LucaKrause1/CICIserlohn/PiScripts/Projection/generateImg/image.png

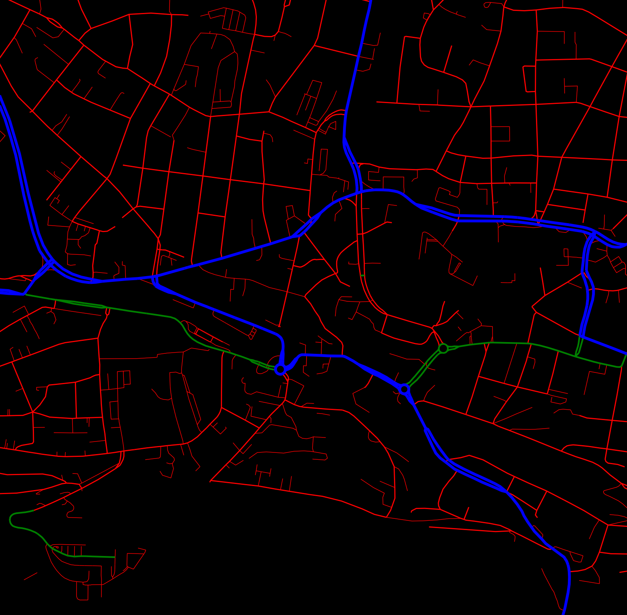
PiScripts/Projection/generateImg/image.png
