LucaKrause1/CICIserlohn/PiScripts/Projection/img/colorAllStreets.png

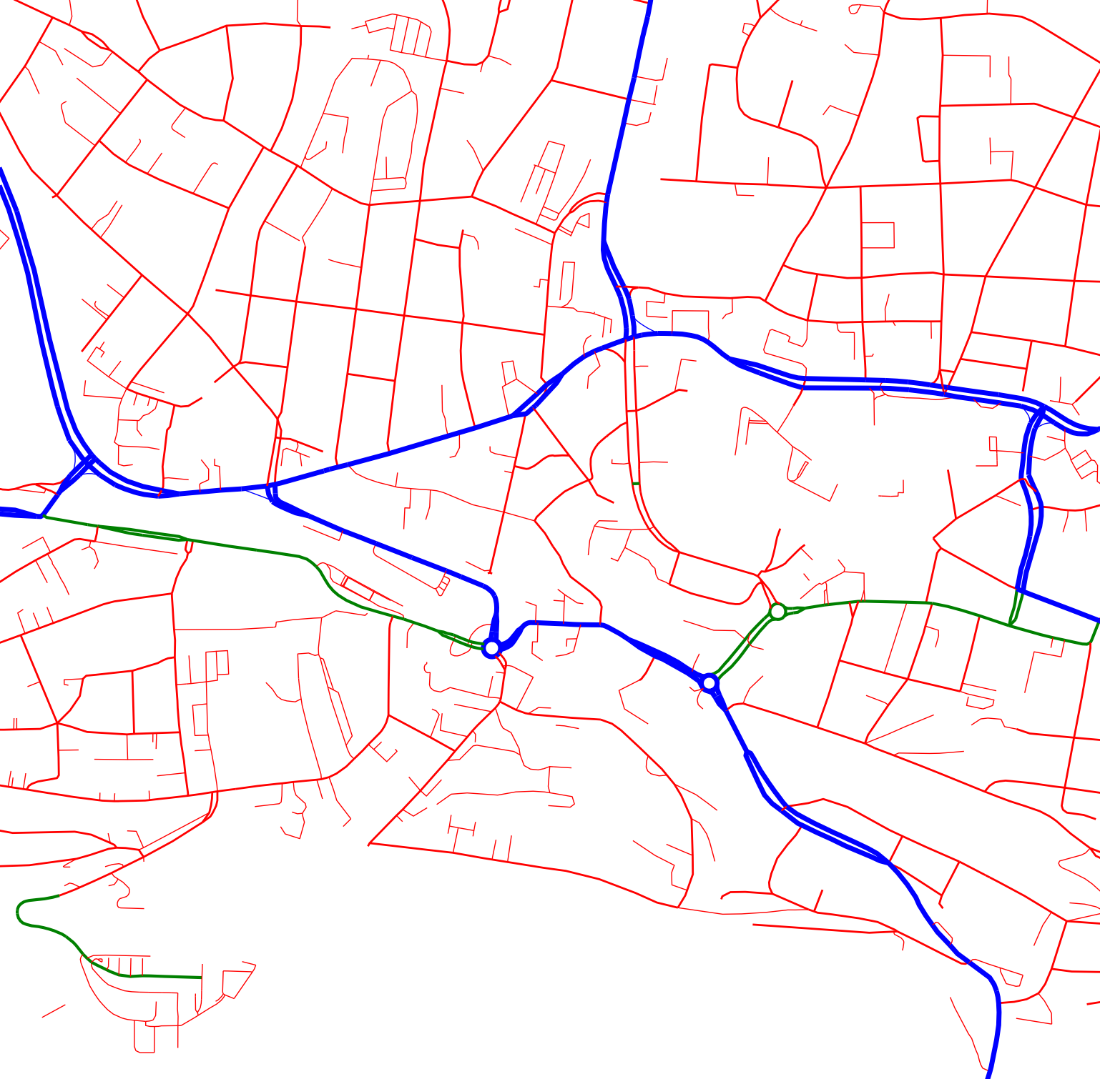
PiScripts/Projection/img/colorAllStreets.png
