LucaKrause1/CICIserlohn/PiScripts/Projection/img/colorBus.png

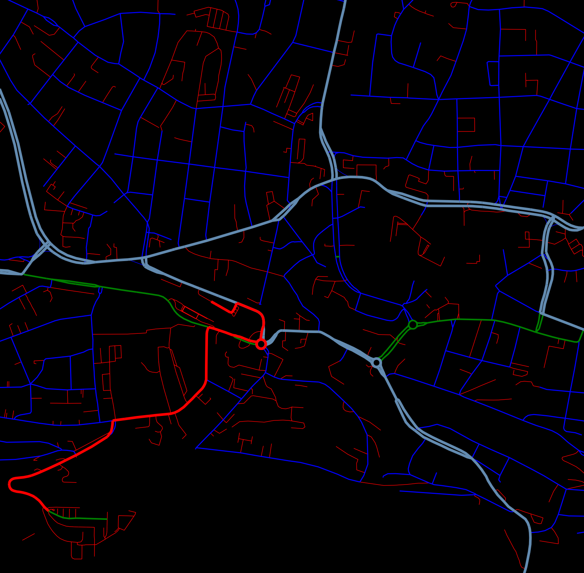
PiScripts/Projection/img/colorBus.png
