LucaKrause1/CICIserlohn/PiScripts/Projection/img/greyTree.png

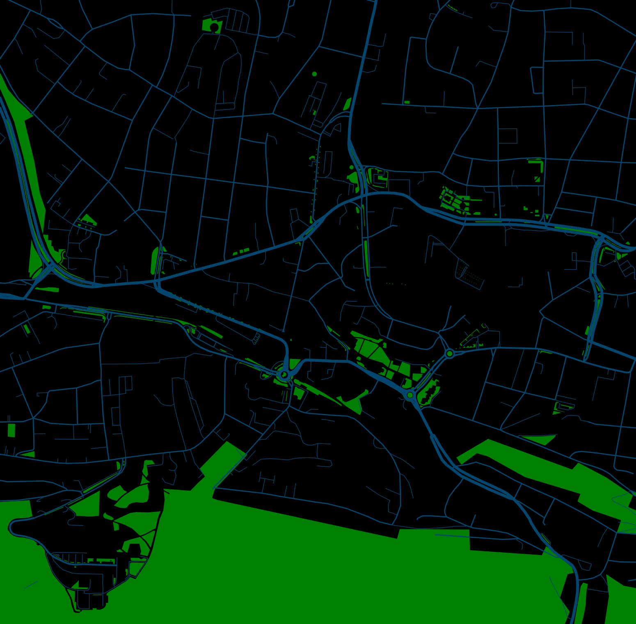
PiScripts/Projection/img/greyTree.png
