LucaKrause1/CICIserlohn/PiScripts/Projection/img/infoabus1.jpg

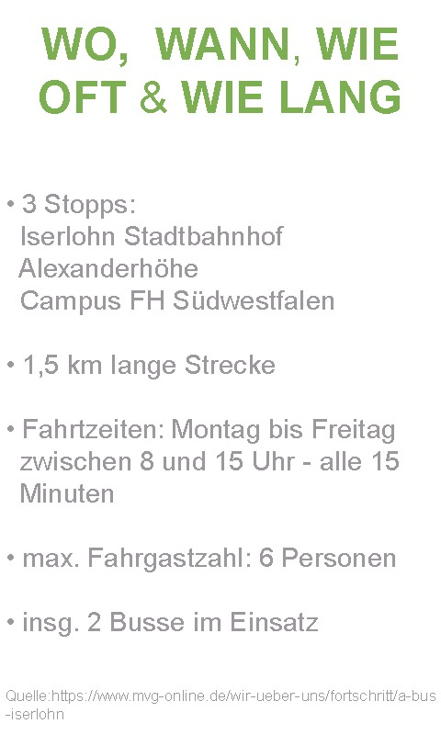
PiScripts/Projection/img/infoabus1.jpg
