LucaKrause1/CICIserlohn/3D-Komponenten/Stadtmodell/13.obj

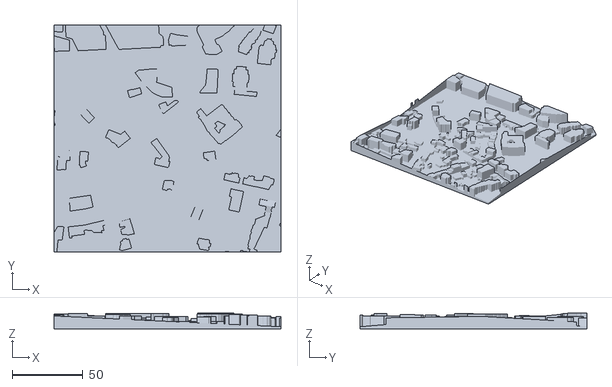
[picture p26: CAD file, 2022-07-13]
3D-Komponenten/Stadtmodell/13.obj
160.1 x 160.0 x 11.3
