LucaKrause1/CICIserlohn/3D-Komponenten/Stadtmodell/12.obj

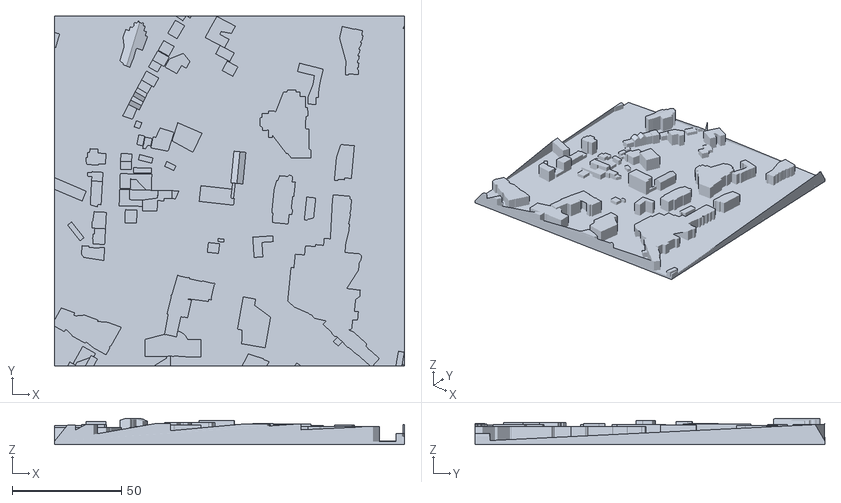
[picture p27: CAD file, 2022-07-13]
3D-Komponenten/Stadtmodell/12.obj
160.1 x 160.1 x 12.1
