LucaKrause1/CICIserlohn/3D-Komponenten/Stadtmodell/6.obj

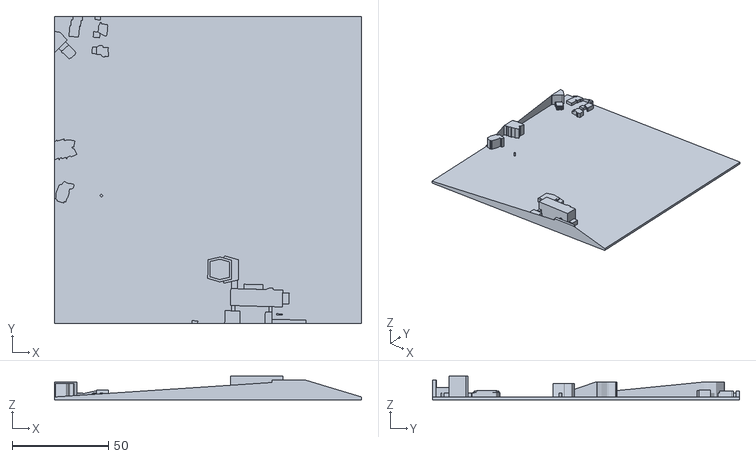
[picture p28: CAD file, 2022-07-13]
3D-Komponenten/Stadtmodell/6.obj
159.8 x 160.0 x 12.5
