LucaKrause1/CICIserlohn/3D-Komponenten/Stadtmodell/11.obj

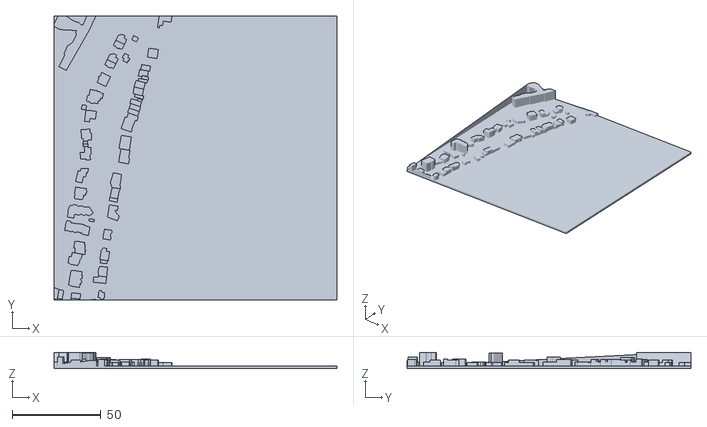
[picture p29: CAD file, 2022-07-13]
3D-Komponenten/Stadtmodell/11.obj
159.7 x 160.0 x 9.20
