LucaKrause1/CICIserlohn/3D-Komponenten/Stadtmodell/18.obj

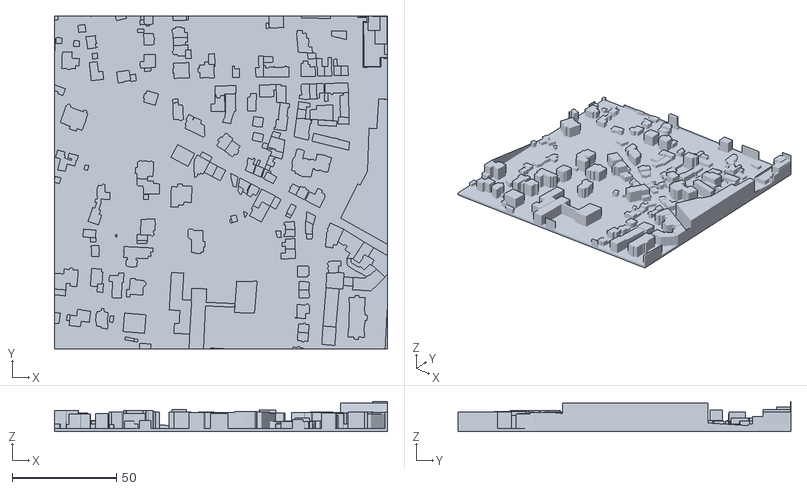
[picture p30: CAD file, 2022-07-13]
3D-Komponenten/Stadtmodell/18.obj
160.1 x 160.0 x 14.6
