LucaKrause1/CICIserlohn/3D-Komponenten/Stadtmodell/8.obj

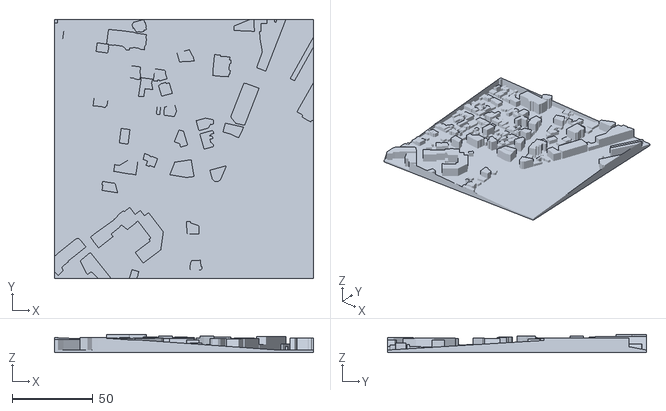
[picture p31: CAD file, 2022-07-13]
3D-Komponenten/Stadtmodell/8.obj
160.1 x 160.1 x 11.3
