LucaKrause1/CICIserlohn/3D-Komponenten/Stadtmodell/16.obj

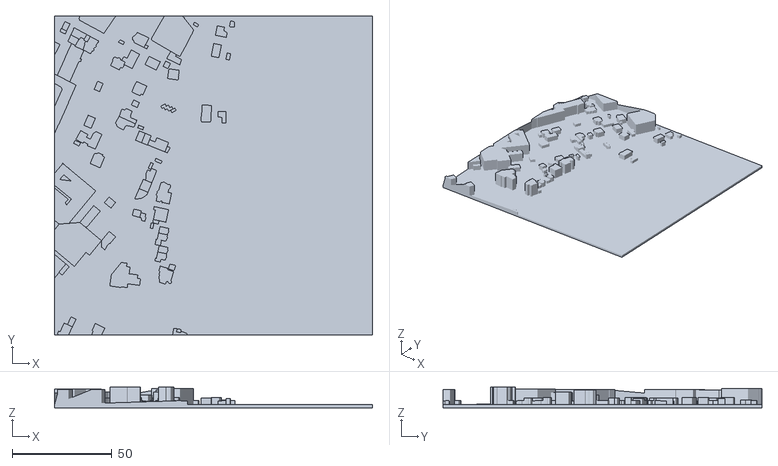
[picture p32: CAD file, 2022-07-13]
3D-Komponenten/Stadtmodell/16.obj
159.7 x 160.0 x 10.4
