LucaKrause1/CICIserlohn/3D-Komponenten/Stadtmodell/4.obj

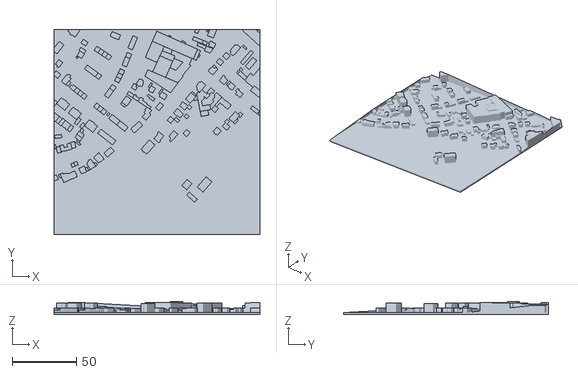
[picture p33: CAD file, 2022-07-13]
3D-Komponenten/Stadtmodell/4.obj
160.1 x 159.5 x 10.3
