LucaKrause1/CICIserlohn/3D-Komponenten/Stadtmodell/3.obj

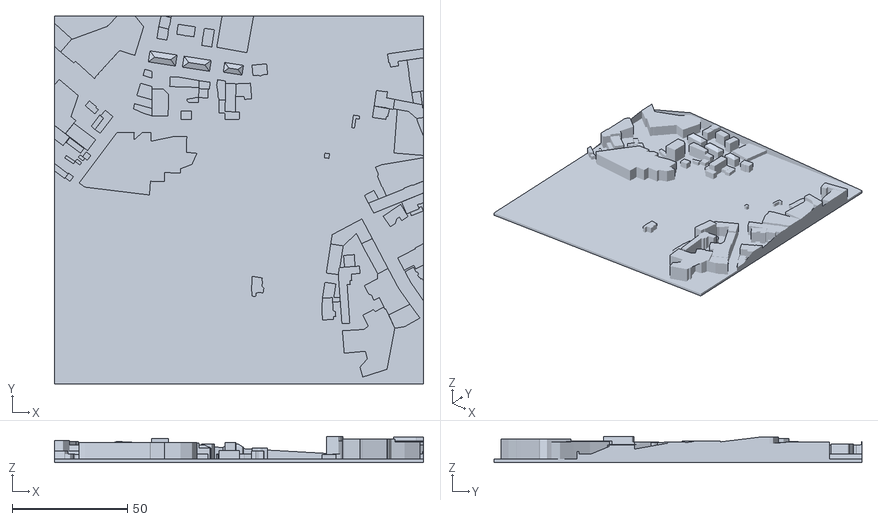
[picture p34: CAD file, 2022-07-13]
3D-Komponenten/Stadtmodell/3.obj
160.0 x 159.5 x 11.4
