LucaKrause1/CICIserlohn/3D-Komponenten/Stadtmodell/24.obj

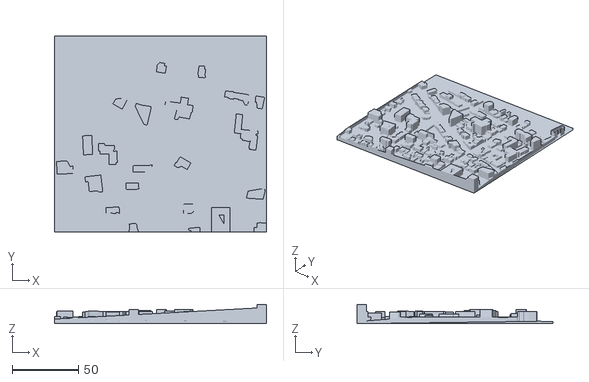
[picture p35: CAD file, 2022-07-13]
3D-Komponenten/Stadtmodell/24.obj
160.0 x 148.1 x 14.6
