LucaKrause1/CICIserlohn/PiScripts/Projection/img/buildings.png

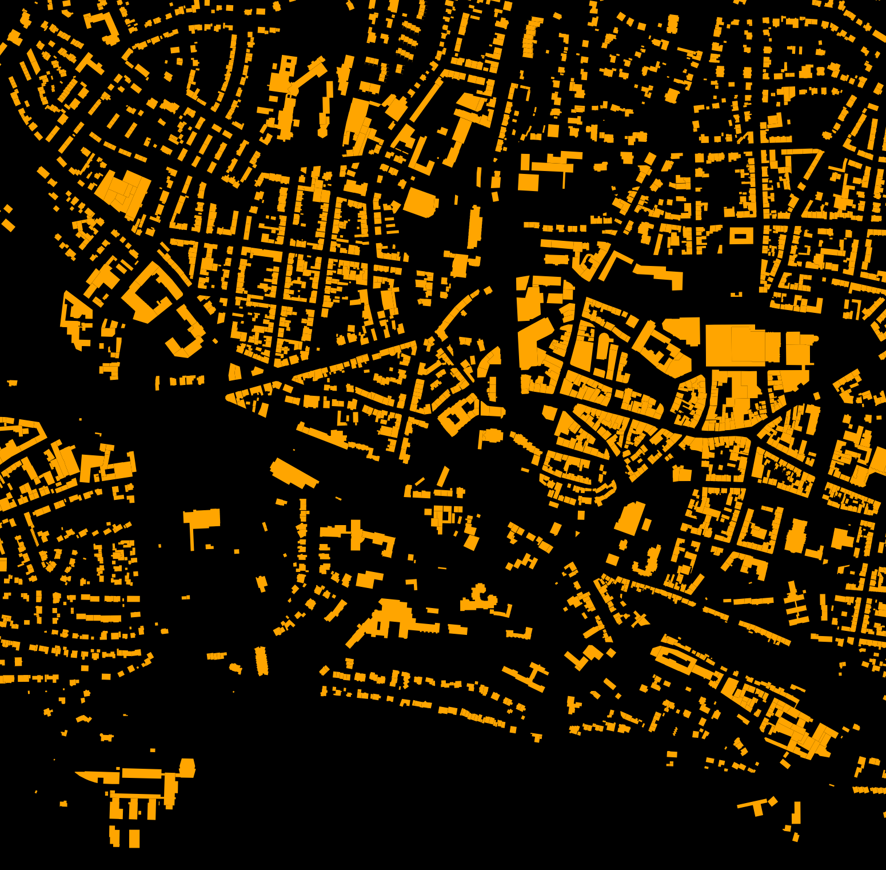
PiScripts/Projection/img/buildings.png
